impatrq/sandtronic/Python/varios/VELOCIMETRO SANDTRONIC THONNY.py

import time
import machine

servo_pin = 13
pwm2 = machine.PWM(machine.Pin(servo_pin))
pwm2.freq(50)

sensor_pin = machine.Pin(20, machine.Pin.IN)
pulse_count = 0
speed = 0.0
diametro= 0.55
circunferencia= 0.55 * 3.14
relacion = 8.9
cant_imanes = 4


servo_duty_0 = 8000
servo_duty_180 = 1333

duty = servo_duty_0

m = (1333-8000) / 80

def calculate_speed(t):
    global pulse_count, speed, duty
    speed = pulse_count * 10 / (relacion * cant_imanes) * circunferencia * 3.6
    duty = int (m * speed + servo_duty_0)
    pulse_count = 0
    print("velocidad: {:.1f} km?h" .format(speed))
    
    
def on_pulse(pin):
    global pulse_count
    pulse_count += 1
    
    
sensor_pin.irq(trigger=machine.Pin.IRQ_RISING,handler=on_pulse)
t= machine.Timer()
t.init(period=100, mode=machine.timer.PERIODIC, callback=calculate_speed)

while True:
    
    print (pulse_count)
    print (speed)
    pwm2.duty_u16(duty)
